stephan192/hoermann_door/esp8266/config_template.h

#define HOSTNAME            "Your hostname"

#define WIFI_SSID           "Your WIFI ssid"
#define WIFI_PASS           "Your WIFI password"

#define MQTT_SERVER         "IP of your MQTT server"
#define MQTT_PORT           1883
#define MQTT_USER           "Your MQTT user"
#define MQTT_PASSWORD       "Your MQTT password"

#define OTA_PASSWORT        "Your OTA password"

#define BME280_I2C_ADR      0x76
